lhm0/rotating_display/RD40_ESP8266/src/RD_40trafo.h

// =========================================================================================================================================
//                                                 Rotating Display RD40
//                                                    © Ludwin Monz
// License: Creative Commons Attribution - Non-Commercial - Share Alike (CC BY-NC-SA)
// you may use, adapt, share. If you share, "share alike".
// you may not use this software for commercial purposes 
// =========================================================================================================================================


#ifndef RD_40trafo_H
#define RD_40trafo_H

// ******************************************************************************************************************************************
//
//          in order to display Bitmaps, the rectangular coordinate system of the 110x110 pixel bitmap needs to be transformed 
//          into the polar coordinate system of the display. The below arrays are lookup-tables for this transformation
//
// ******************************************************************************************************************************************

const char trafo_x[40][240] PROGMEM = {
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
};

#endif  
