lhm0/rotating_display/RD40_ESP8266/src/my_BMPtemplates.h

// =========================================================================================================================================
//                                                 Rotating Display RD40
//                                                    © Ludwin Monz
// License: Creative Commons Attribution - Non-Commercial - Share Alike (CC BY-NC-SA)
// you may use, adapt, share. If you share, "share alike".
// you may not use this software for commercial purposes 
// =========================================================================================================================================


#ifndef my_BMPtemplates_H
#define my_BMPtemplates_H

// +++++++++++++++++++++++++++++++++++++++++++++++++++++++++++++++++++++++++++++++++++++++++++++++++++++++++++++++++++++++
// numerical character set 16x24. Contains numbers 0....9 and ":" character. Each of the 36 columns has 7 bytes (36x7=252)
// +++++++++++++++++++++++++++++++++++++++++++++++++++++++++++++++++++++++++++++++++++++++++++++++++++++++++++++++++++++++
const char chr_16x24[11][48] PROGMEM =
{{0x00, 0x00, 0x00, 0xE0, 0xFF, 0x07, 0xF8, 0xFF, 0x1F, 0x3C, 0x00, 0x3C, 0x0E, 0x00, 0x70, 0x06, 0x00, 0x60, 0x07, 0x00, 0xE0, 0x03, 0x00, 0xC0, 0x03, 0x00, 0xC0, 0x07, 0x00, 0xE0, 0x06, 0x00, 0x60, 0x0E, 0x00, 0x70, 0x3C, 0x00, 0x3C, 0xF8, 0xFF, 0x1F, 0xE0, 0xFF, 0x07, 0x00, 0x00, 0x00},
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
 {{0x00, 0x00, 0x00}, {0x00, 0x00, 0x00}, {0x00, 0x00, 0x00}, {0x00, 0x30, 0x01}, {0x00, 0x30, 0x01}, {0x00, 0x30, 0x01}, {0x00, 0x30, 0x01}, {0x60, 0x33, 0x81}, {0x60, 0x33, 0x81}, {0x60, 0x33, 0x81}, {0x60, 0x33, 0x99}, {0x66, 0x33, 0x99}, {0x66, 0x33, 0x99}, {0x66, 0x33, 0x99}, {0x66, 0x33, 0x99}, {0x66, 0x33, 0x99}, {0x66, 0x33, 0x99}, {0x66, 0x33, 0x99}, {0x66, 0x33, 0x19}, {0x60, 0x03, 0x18}, {0x60, 0x03, 0x18}, {0x60, 0x03, 0x18}, {0x60, 0x03, 0x18}, {0x00, 0x00, 0x18}, {0x00, 0x00, 0x18}, {0x00, 0x00, 0x18}, {0x00, 0x00, 0x18}, {0x00, 0x00, 0x00}, {0x00, 0x00, 0x00}, {0x00, 0x00, 0x00}}};
 
#endif  
