lhm0/rotating_display/RD40_ESP8266/src/webinterface_data.h

#include <Arduino.h>

const char timeZones[4][37][50] PROGMEM =
{{"Alaska", "America Samoa", "Argentina", "Azerbaijan", "Bangladesh", "Cabo Verde", "Central Australia", "Chatham Islands", "Chicago, Illinois", "China", "Christmas Island", "Denver, Colorado", "Eastern Australia", "French Polynesia", "Germany", "Greece", "Greenland", "Hawaii", "Iceland", "India", "Indonesia", "Iran", "Japan", "Lord Howe Island", "Los Angeles", "Myanmar", "Nepal", "New York", "New Zealand", "Newfoundland", "Pakistan", "Phoenix, Arizona", "Solomon Islands", "Tonga", "UK", "US Baker Island","Western Australia"},
 {"AKST/AKDT", "NUT", "ART", "GST", "BST", "CVT", "ACST/ACDT", "CHAST/CHADT", "CST/CDT", "CST", "LINT", "MST", "AEST/AEDT", "MART", "CEST/CET", "MSK", "WGST/WGT", "HST/HDT", "GMT", "IST", "WIB", "IRDT/IRST", "JST", "LHST/LHDT", "PDT", "MMT", "NPT", "EST/EDT", "ANAT", "NDT/NST", "UZT", "MST", "SBT", "TOT/TOST", "BST/GMT", "AoE", "ACWST"},
 {"UTC -9", "UTC -11", "UTC -3", "UTC +4", "UTC +6", "UTC -1", "UTC +9:30", "UTC +12:45", "UTC -6", "UTC +8", "UTC +14", "UTC -7", "UTC +10", "UTC -9:30", "UTC +2", "UTC +3", "UTC -2", "UTC -10", "UTC +0", "UTC +5:30", "UTC +7", "UTC +4:30", "UTC +9", "UTC +10:30", "UTC -8", "UTC +6:30", "UTC +5:45", "UTC -5", "UTC +12", "UTC -2:30", "UTC +5", "UTC -7", "UTC +11", "UTC +13", "UTC +1", "UTC -12", "UTC +8:45"},
 {"ASKT9AKDT,M3.2.0/2:00:00,M11.1.0/2:00:00", "NUT11", "ART3", "GST-4", "BST-6", "CVT1", "ACST-8:30ACDT,M3.2.0/2:00:00,M11.1.0/2:00:00", "CHAST-11:45CHADT,M3.2.0/2:00:00,M11.1.0/2:00:00", "CST6CDT,M3.2.0/2:00:00,M11.1.0/2:00:00", "CST-8", "LINT-14", "MST7MDT,M3.2.0/2:00:00,M11.1.0/2:00:00", "AEST-9AEDT,M3.2.0/2:00:00,M11.1.0/2:00:00", "MART9:30,M3.2.0/2:00:00,M11.1.0/2:00:00", "CEST-1CET,M3.5.0/2:00:00,M10.5.0/3:00:00", "MSK-3", "WGST3WGT,M3.2.0/2:00:00,M11.1.0/2:00:00", "HST11HDT,M3.2.0/2:00:00,M11.1.0/2:00:00", "GMT+0", "IST-5:30", "WIB-7", "IRDT-3:30IRST,M3.2.0/2:00:00,M11.1.0/2:00:00", "JST-9", "LHST-9:30LHDT,M3.2.0/2:00:00,M11.1.0/2:00:00", "PST8PDT,M3.2.0/2:00:00,M11.1.0/2:00:00", "MMT-6:30", "NPT-5:45", "EST5EDT,M3.2.0/2:00:00,M11.1.0/2:00:00", "ANAT-12", "NDT3:30NST,M3.2.0/2:00:00,M11.1.0/2:00:00", "UZT-5", "MST7", "SBT-11", "TOT-12TOST,M3.2.0/2:00:00,M11.1.0/2:00:00", "BST0GMT,M3.2.0/2:00:00,M11.1.0/2:00:00", "AOE12", "ACWST-8:45"}};
