lhm0/rotating_display/RD40_simple/RD40_simple_ESP8266/src/tables.h

#ifndef TABLES_H
#define TABLES_H

#include <avr/pgmspace.h>  // PROGMEM-Unterstützung

extern const char trafo_x[40][240] PROGMEM;
extern const char trafo_y[40][240] PROGMEM;
extern const char chr_12x18[96][36] PROGMEM;
extern const char chr_10x15[96][20] PROGMEM;

#endif  // TABLES_H
